rertzer/MoovUp/toPrint/forarm/robpart2V4.stl

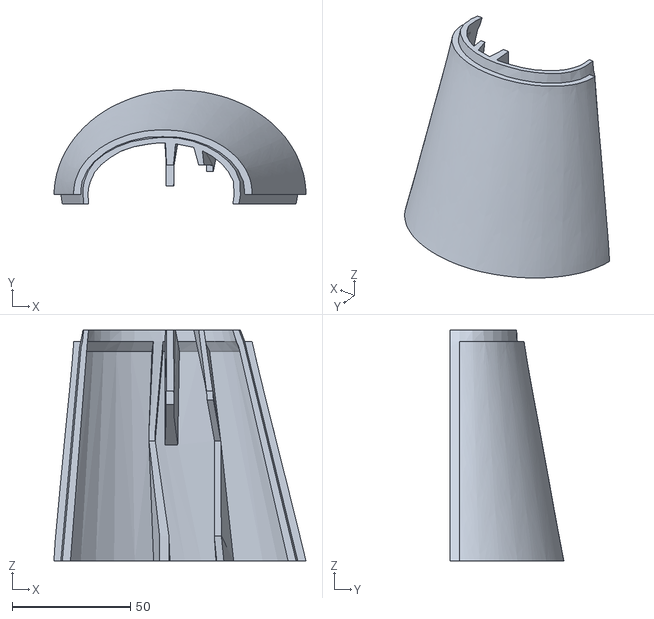
[picture p16: CAD file, 2025-05-26]
toPrint/forarm/robpart2V4.stl
106.4 x 48.1 x 97.5
