rertzer/MoovUp/toPrint/hand/i2_WristLargeV2.stl

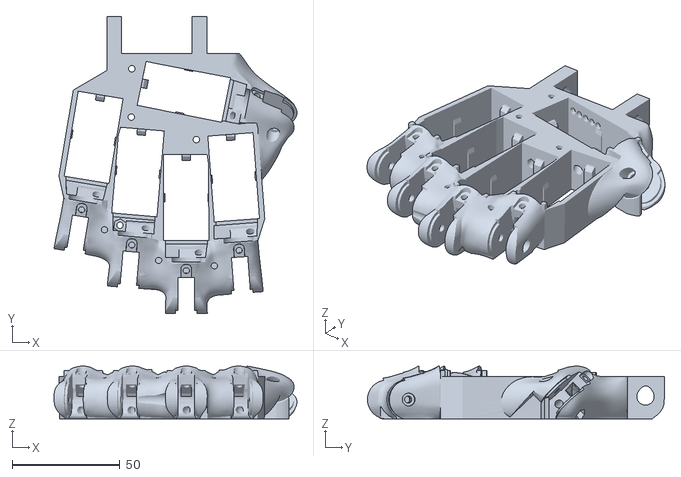
[picture p17: CAD file, 2025-05-26]
toPrint/hand/i2_WristLargeV2.stl
112.6 x 137.7 x 24.5
