rertzer/MoovUp/toPrint/motor/motorAdaptor.stl

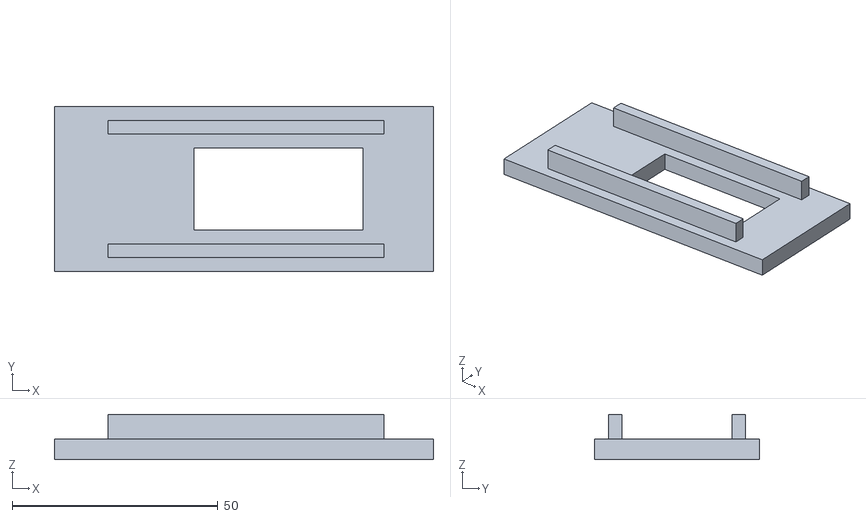
[picture p18: CAD file, 2025-06-15]
toPrint/motor/motorAdaptor.stl
92.0 x 40.0 x 11.0
