rertzer/MoovUp/toPrint/shoulder/PivMitV2.stl

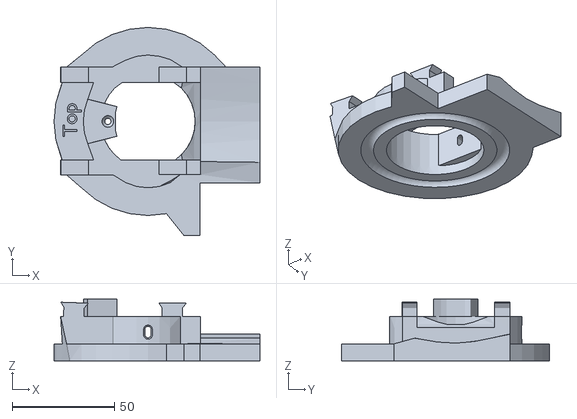
[picture p19: CAD file, 2025-06-15]
toPrint/shoulder/PivMitV2.stl
100.6 x 101.6 x 30.2
