rertzer/MoovUp/toPrint/wrist/RotaWrist3V3.stl

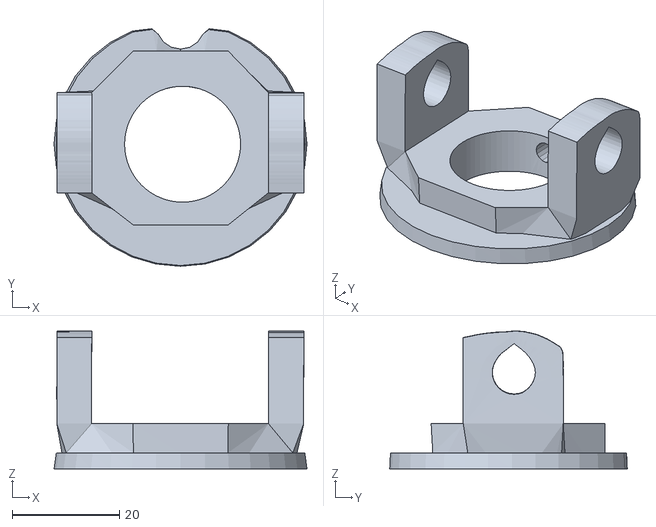
[picture p20: CAD file, 2025-05-26]
toPrint/wrist/RotaWrist3V3.stl
47.2 x 44.3 x 25.7
