rertzer/MoovUp/toPrint/bicep/RotWormV5.stl

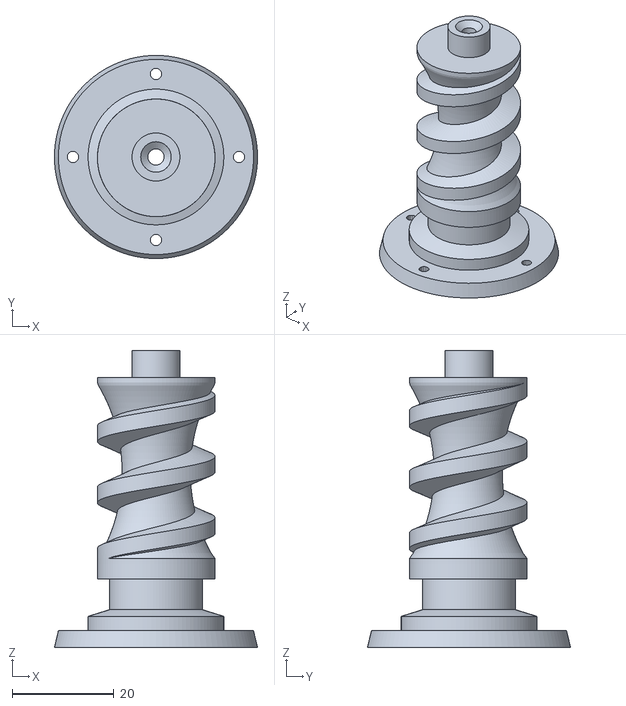
[picture p21: CAD file, 2025-05-26]
toPrint/bicep/RotWormV5.stl
40.0 x 39.9 x 58.4
