rertzer/MoovUp/toPrint/extra/entretoise.stl

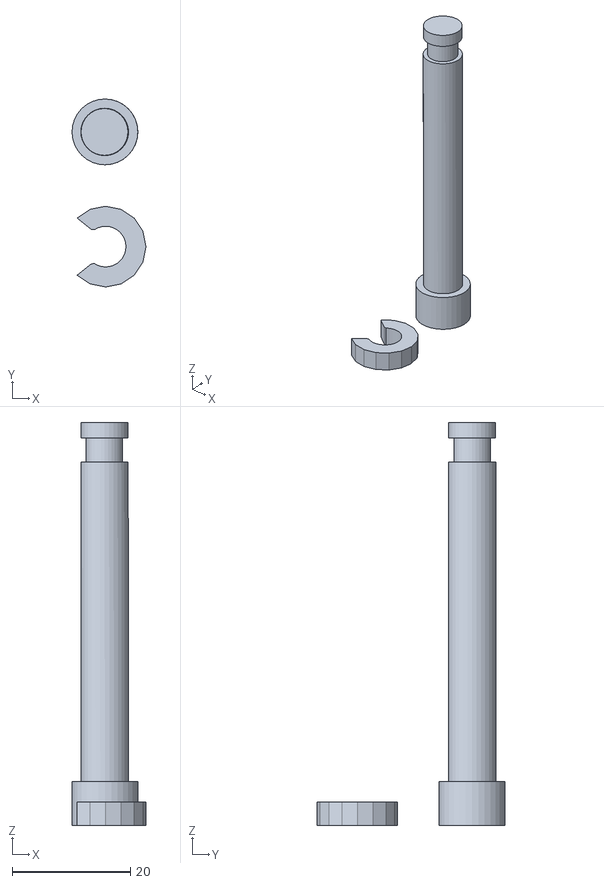
[picture p22: CAD file, 2025-06-15]
toPrint/extra/entretoise.stl
12.5 x 31.8 x 68.1
