rertzer/MoovUp/toPrint/forarm/RobRingV3.stl

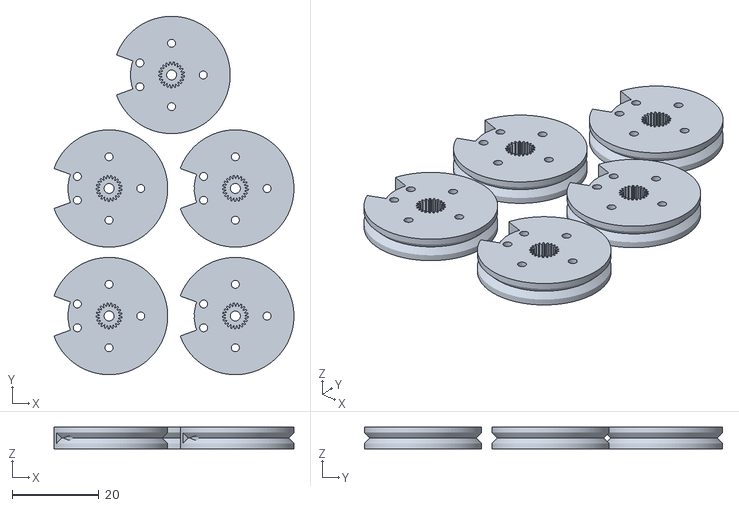
[picture p23: CAD file, 2025-05-26]
toPrint/forarm/RobRingV3.stl
55.3 x 82.5 x 5.00
