rertzer/MoovUp/toPrint/hand/color/i2_HandCoverV2.stl

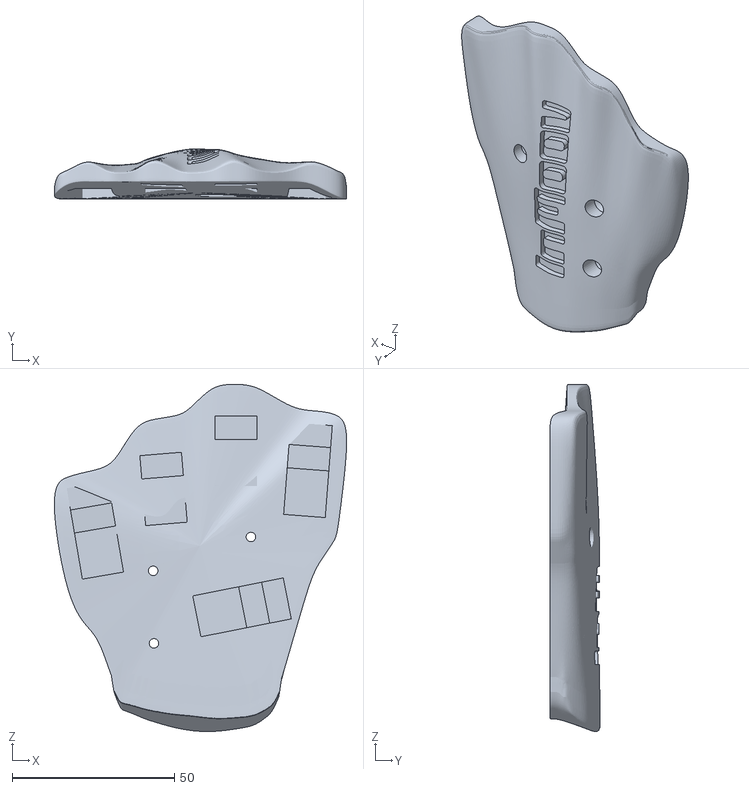
[picture p24: CAD file, 2025-05-26]
toPrint/hand/color/i2_HandCoverV2.stl
90.2 x 15.6 x 107.1
