rertzer/MoovUp/toPrint/hand/i2_FingersX5V2.stl

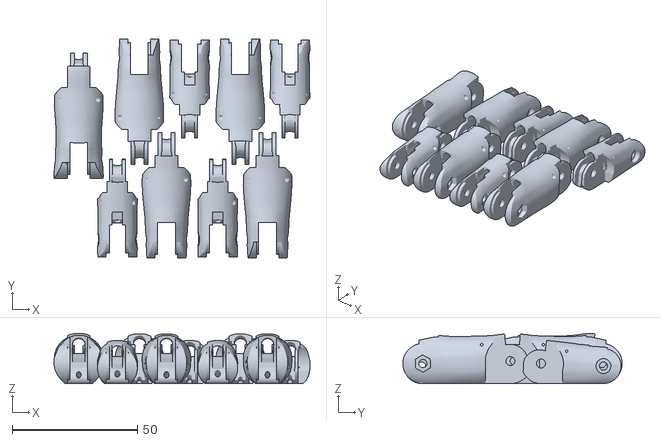
[picture p25: CAD file, 2025-05-26]
toPrint/hand/i2_FingersX5V2.stl
102.3 x 87.7 x 20.0
