rertzer/MoovUp/toPrint/motor/servoDiskShoulder.stl

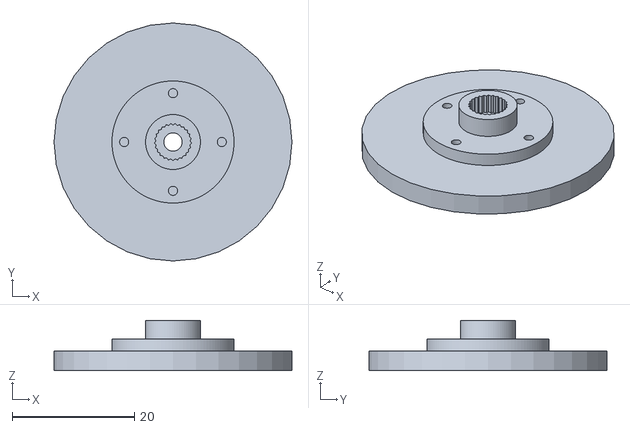
[picture p26: CAD file, 2025-06-15]
toPrint/motor/servoDiskShoulder.stl
39.0 x 39.0 x 8.20
