rertzer/MoovUp/toPrint/wrist/RotaWrist2V3.stl

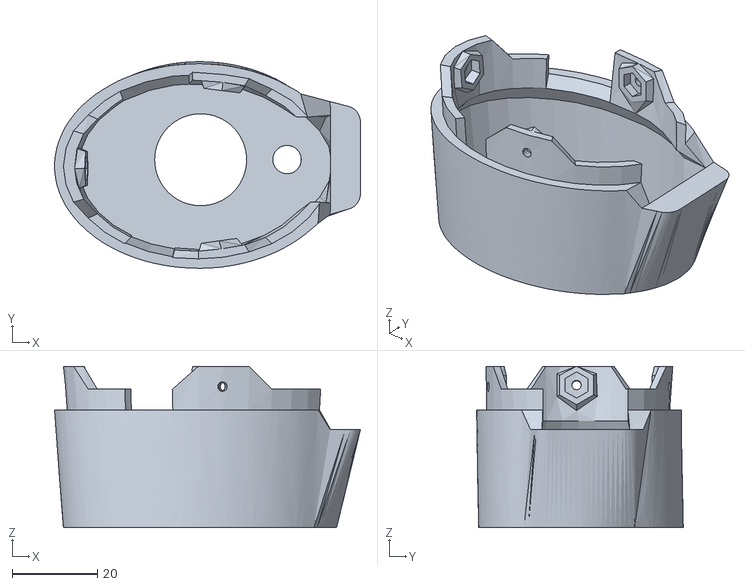
[picture p27: CAD file, 2025-05-26]
toPrint/wrist/RotaWrist2V3.stl
71.9 x 48.6 x 38.0
