rertzer/MoovUp/toPrint/bicep/HighArmSideV3.stl

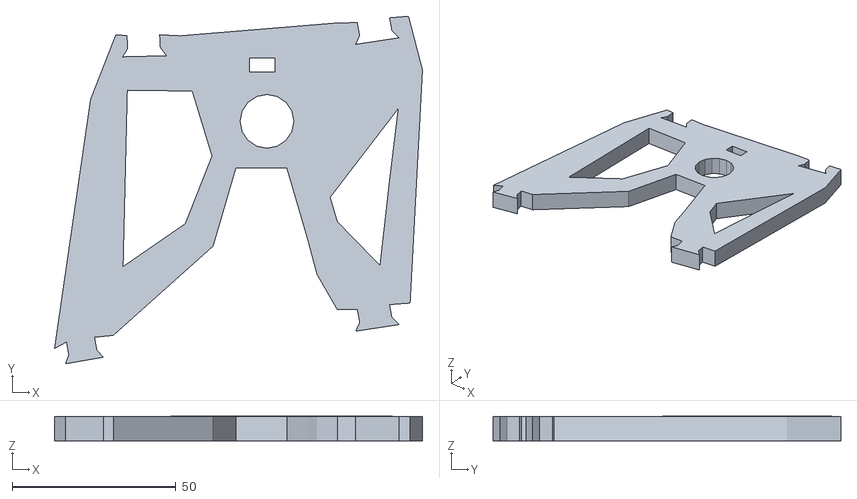
[picture p28: CAD file, 2025-05-26]
toPrint/bicep/HighArmSideV3.stl
112.4 x 106.1 x 7.50
