rertzer/MoovUp/toPrint/forarm/TensionerRightV1.stl

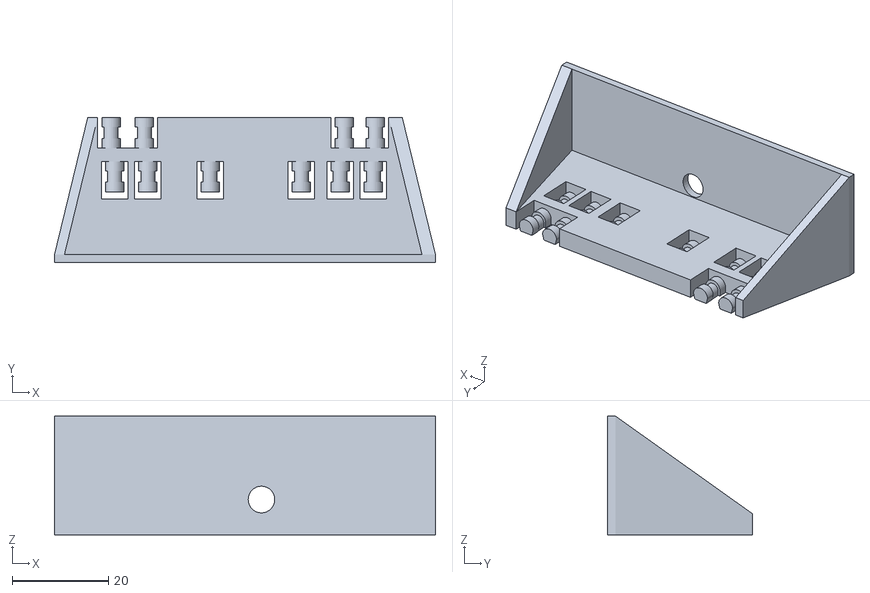
[picture p29: CAD file, 2025-05-26]
toPrint/forarm/TensionerRightV1.stl
79.3 x 30.3 x 24.7
