rertzer/MoovUp/toPrint/hand/color/i2_CoverFingerV3.stl

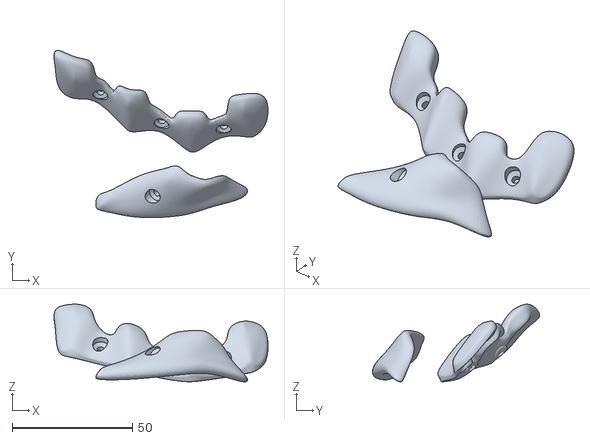
[picture p30: CAD file, 2025-05-26]
toPrint/hand/color/i2_CoverFingerV3.stl
89.0 x 69.6 x 32.3
