rertzer/MoovUp/toPrint/hand/i2_WristGearV1.stl

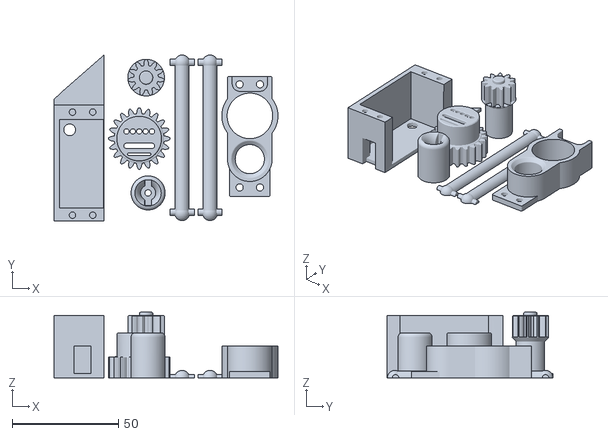
[picture p31: CAD file, 2025-05-26]
toPrint/hand/i2_WristGearV1.stl
105.2 x 78.1 x 30.8
