rertzer/MoovUp/toPrint/motor/motorAdaptorBis.stl

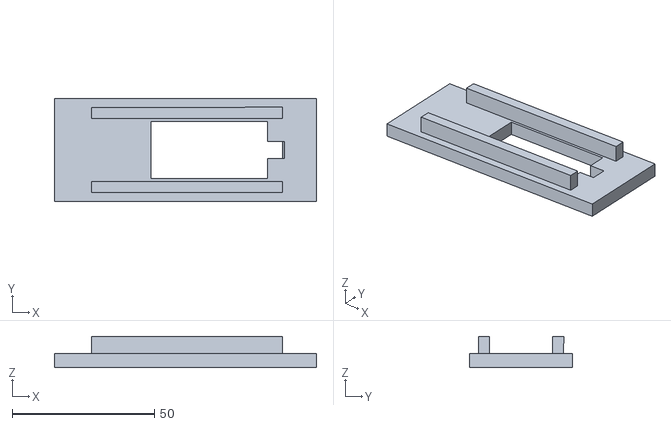
[picture p32: CAD file, 2025-06-15]
toPrint/motor/motorAdaptorBis.stl
92.0 x 36.0 x 11.0
