rertzer/MoovUp/toPrint/wrist/RotaWrist1V4.stl

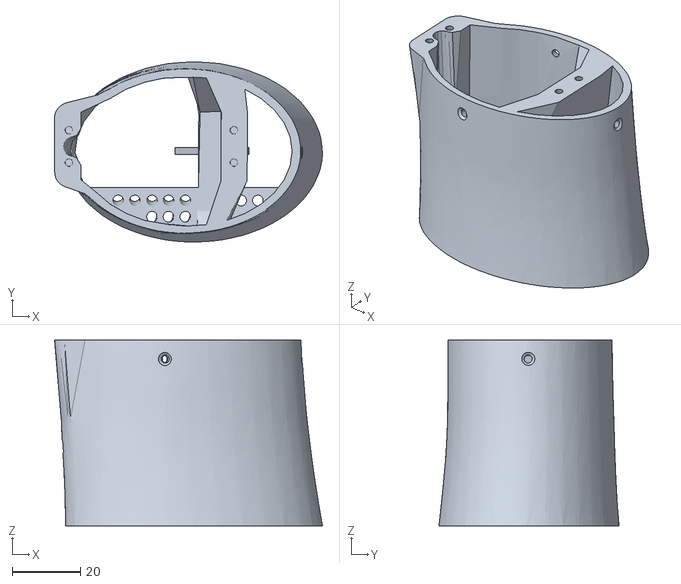
[picture p33: CAD file, 2025-05-26]
toPrint/wrist/RotaWrist1V4.stl
78.6 x 52.8 x 54.5
