rertzer/MoovUp/toPrint/bicep/PistonanticlockV2.stl

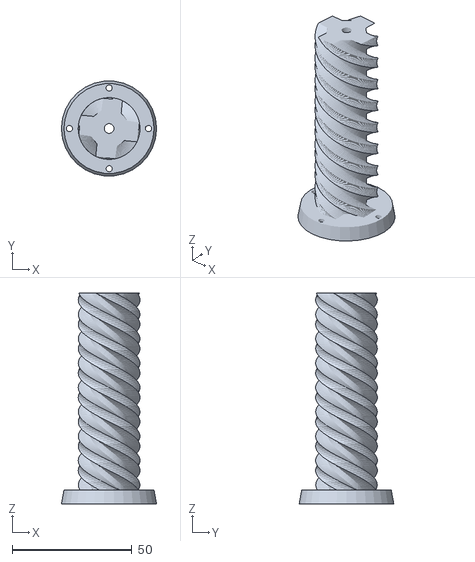
[picture p34: CAD file, 2025-05-26]
toPrint/bicep/PistonanticlockV2.stl
39.7 x 39.5 x 88.0
