rertzer/MoovUp/toPrint/forarm/RobCableBackV3.stl

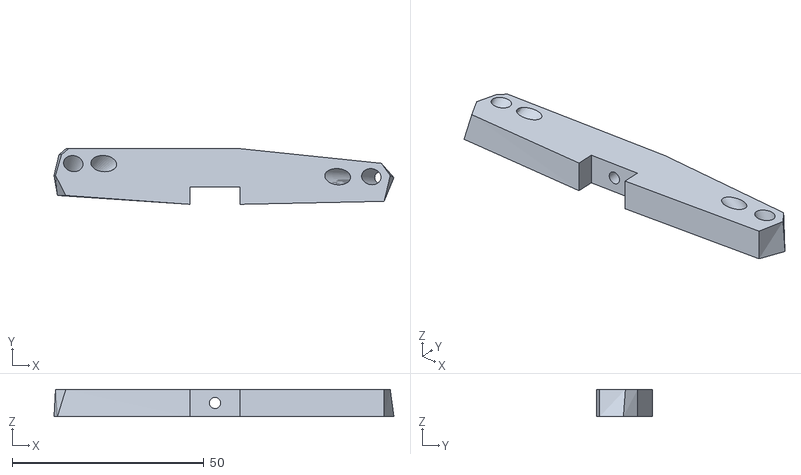
[picture p35: CAD file, 2025-05-26]
toPrint/forarm/RobCableBackV3.stl
88.7 x 14.5 x 7.17
