rertzer/MoovUp/toPrint/hand/i2_PulleyX5V1.stl

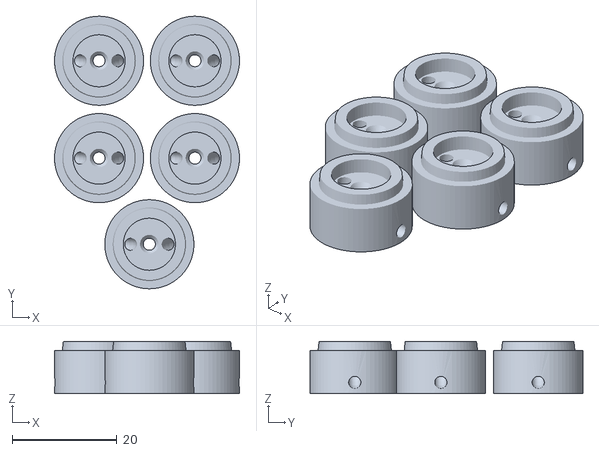
[picture p36: CAD file, 2025-05-26]
toPrint/hand/i2_PulleyX5V1.stl
35.3 x 52.0 x 10.0
