rertzer/MoovUp/toPrint/wrist/CableHolderWristV5.stl

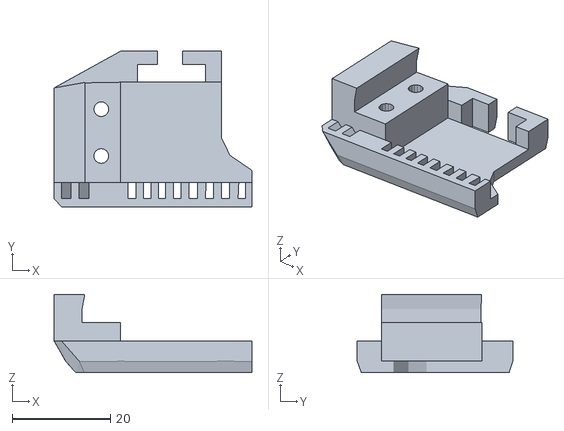
[picture p37: CAD file, 2025-05-26]
toPrint/wrist/CableHolderWristV5.stl
40.2 x 31.6 x 15.8
