rertzer/MoovUp/toPrint/bicep/PivPotentioRoundV3.stl

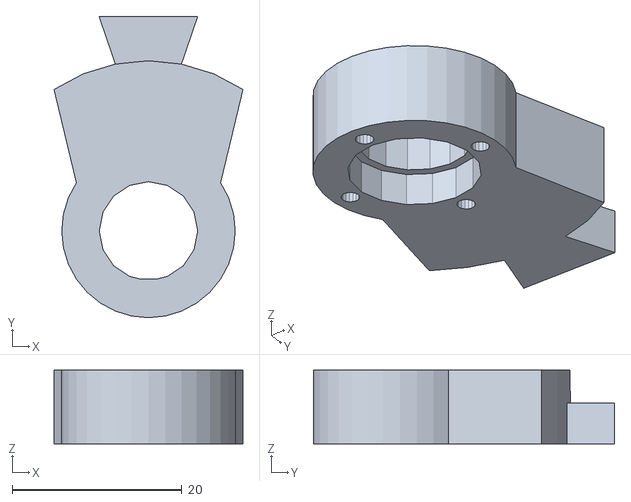
[picture p38: CAD file, 2025-05-26]
toPrint/bicep/PivPotentioRoundV3.stl
22.3 x 35.5 x 8.68
