rertzer/MoovUp/toPrint/forarm/robpart5V4.stl

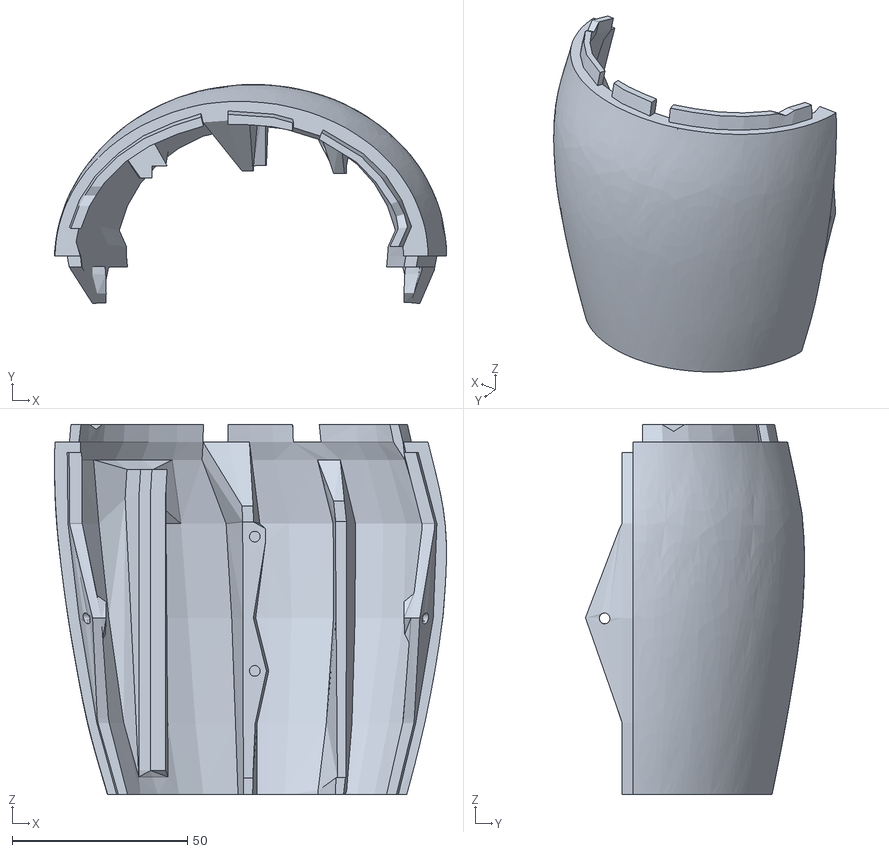
[picture p39: CAD file, 2025-05-26]
toPrint/forarm/robpart5V4.stl
111.8 x 62.5 x 105.6
