rertzer/MoovUp/toPrint/bicep/servobaseV1.stl

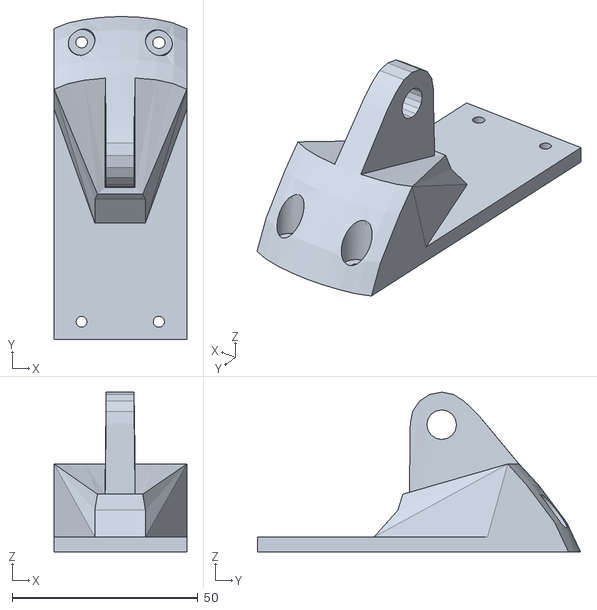
[picture p40: CAD file, 2025-05-26]
toPrint/bicep/servobaseV1.stl
35.7 x 87.0 x 43.1
