rertzer/MoovUp/toPrint/forarm/servo-pulleyX5.stl

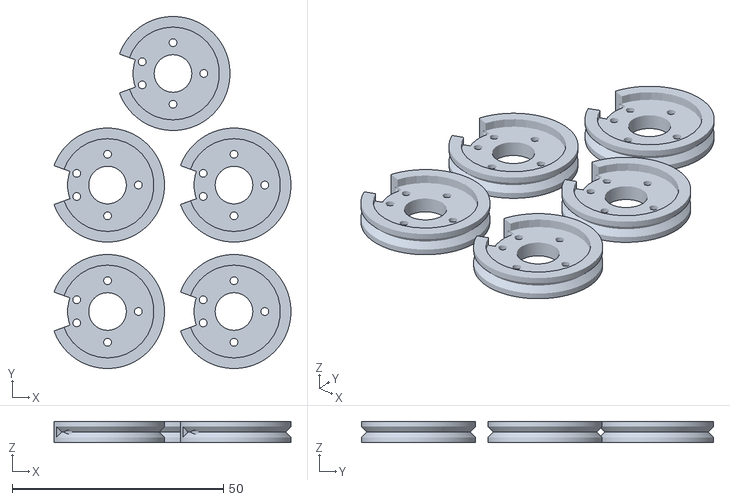
[picture p41: CAD file, 2025-05-26]
toPrint/forarm/servo-pulleyX5.stl
56.1 x 83.4 x 5.00
