rertzer/MoovUp/toPrint/bicep/elbowshaftgearV1.stl

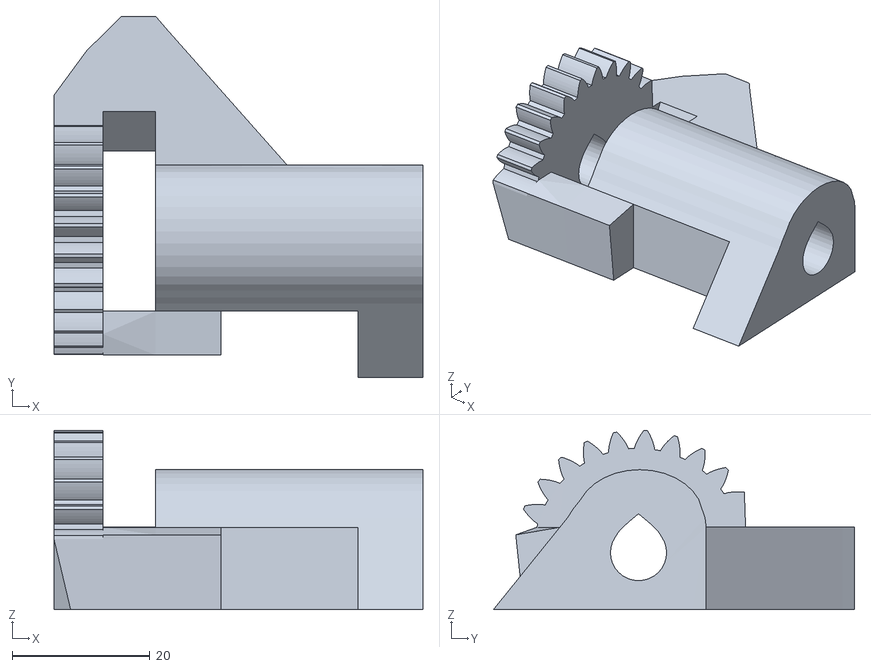
[picture p42: CAD file, 2025-05-26]
toPrint/bicep/elbowshaftgearV1.stl
53.5 x 52.4 x 26.0
