rertzer/MoovUp/toPrint/forarm/RobCableFrontV3.stl

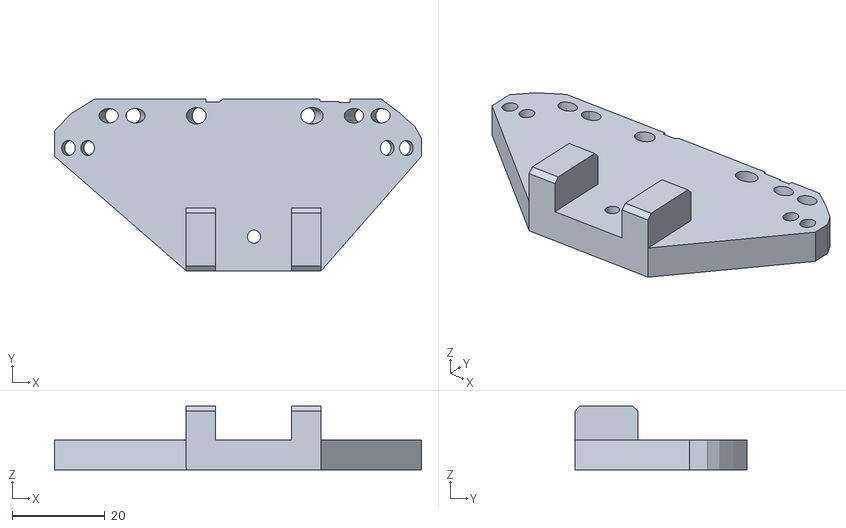
[picture p43: CAD file, 2025-05-26]
toPrint/forarm/RobCableFrontV3.stl
79.3 x 37.1 x 13.8
