rertzer/MoovUp/toPrint/bicep/armtopcover1.stl

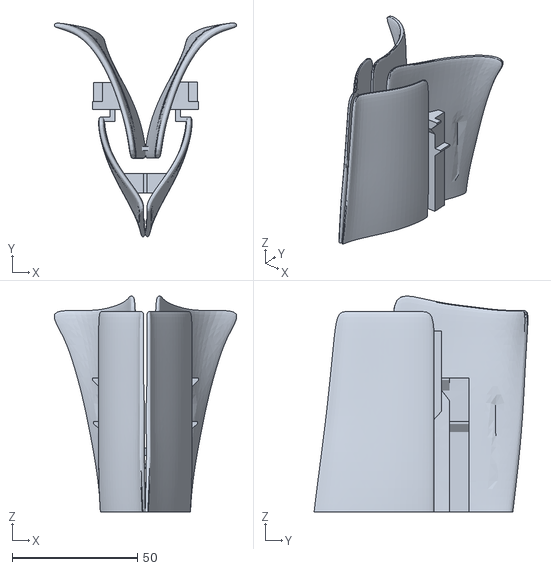
[picture p44: CAD file, 2025-05-26]
toPrint/bicep/armtopcover1.stl
72.7 x 85.2 x 86.1
