rertzer/MoovUp/toPrint/forarm/robcap3V2.stl

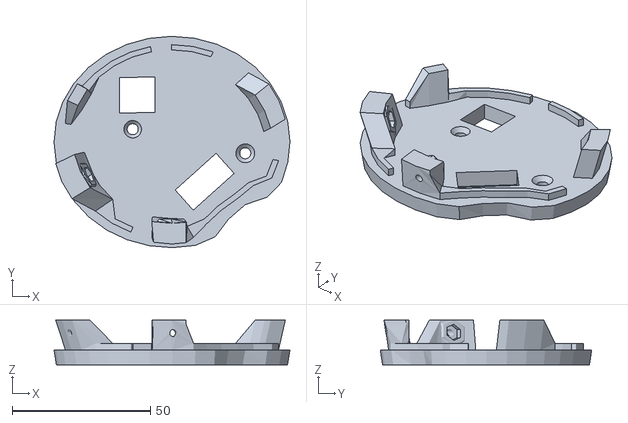
[picture p45: CAD file, 2025-05-26]
toPrint/forarm/robcap3V2.stl
85.5 x 76.5 x 16.2
