rertzer/MoovUp/toPrint/bicep/RotcenterV3.stl

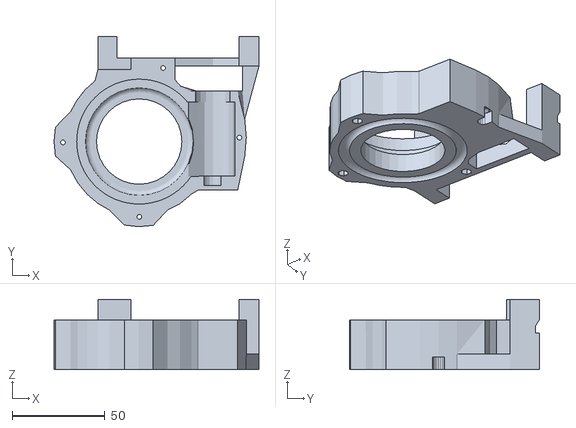
[picture p46: CAD file, 2025-05-26]
toPrint/bicep/RotcenterV3.stl
110.5 x 102.6 x 37.8
