rertzer/MoovUp/toPrint/forarm/RobServoBedV6.stl

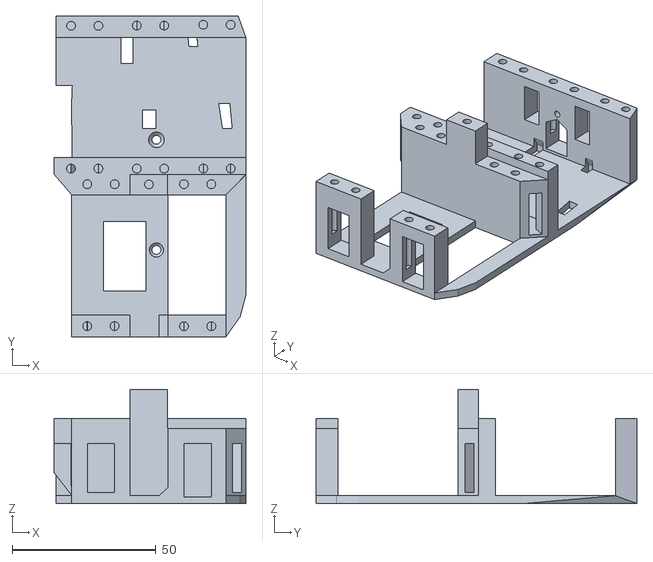
[picture p47: CAD file, 2025-05-26]
toPrint/forarm/RobServoBedV6.stl
66.7 x 111.6 x 39.7
