rertzer/MoovUp/toPrint/bicep/RotMitV3.stl

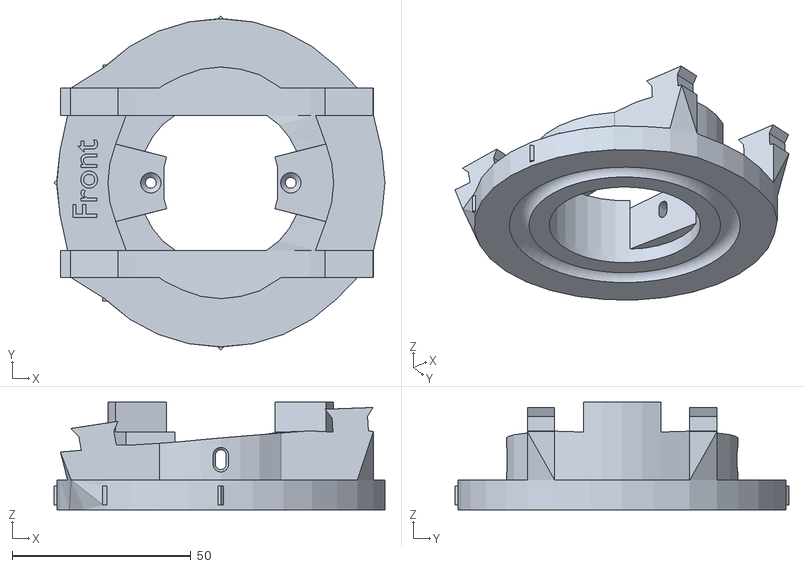
[picture p48: CAD file, 2025-05-26]
toPrint/bicep/RotMitV3.stl
92.6 x 93.4 x 30.2
