rertzer/MoovUp/toPrint/forarm/robpart3V4.stl

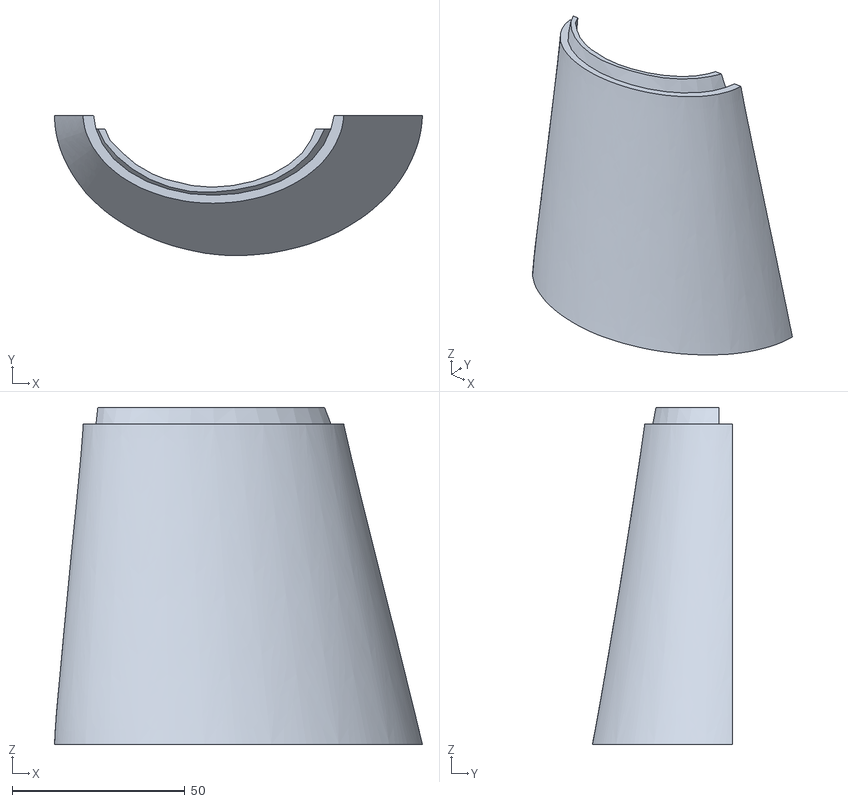
[picture p49: CAD file, 2025-05-26]
toPrint/forarm/robpart3V4.stl
106.4 x 40.6 x 97.5
