rertzer/MoovUp/toPrint/bicep/servoholderV1.stl

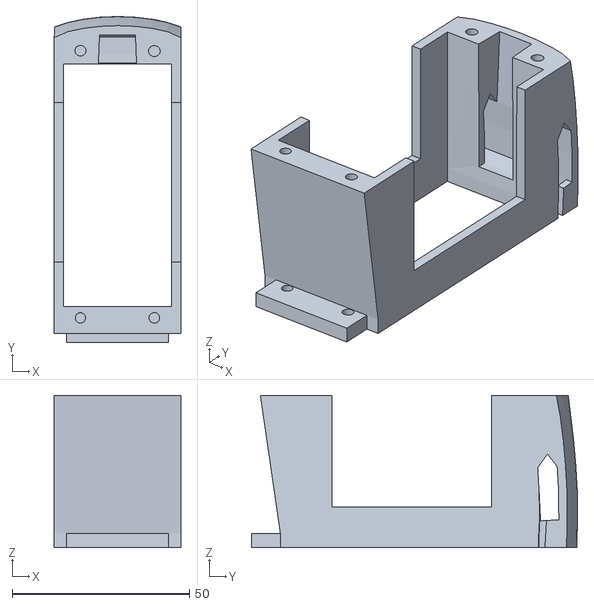
[picture p50: CAD file, 2025-05-26]
toPrint/bicep/servoholderV1.stl
35.8 x 91.9 x 42.9
