rertzer/MoovUp/toPrint/bicep/spacerV1.stl

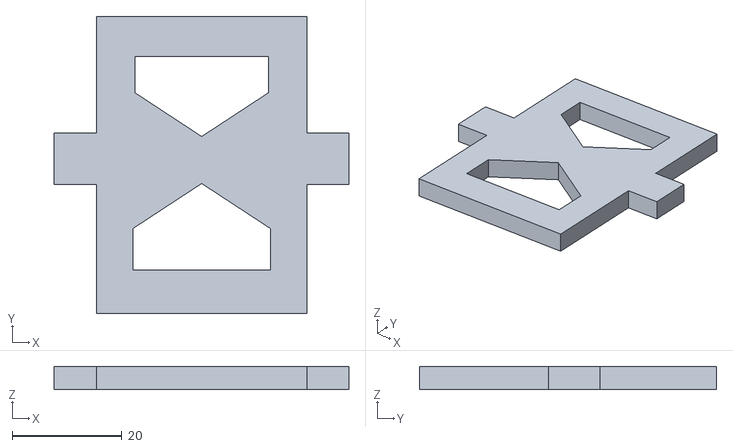
[picture p51: CAD file, 2025-05-26]
toPrint/bicep/spacerV1.stl
53.8 x 54.3 x 4.23
