rertzer/MoovUp/toPrint/bicep/ReinforcerV2.stl

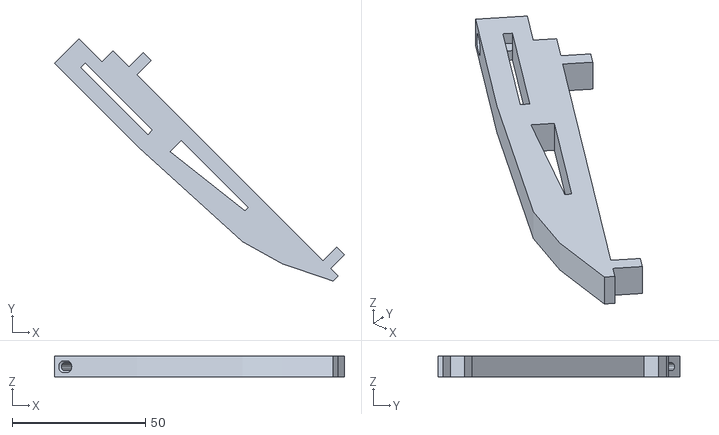
[picture p52: CAD file, 2025-05-26]
toPrint/bicep/ReinforcerV2.stl
108.8 x 90.9 x 7.77
