rertzer/MoovUp/toPrint/bicep/RotGearV6.stl

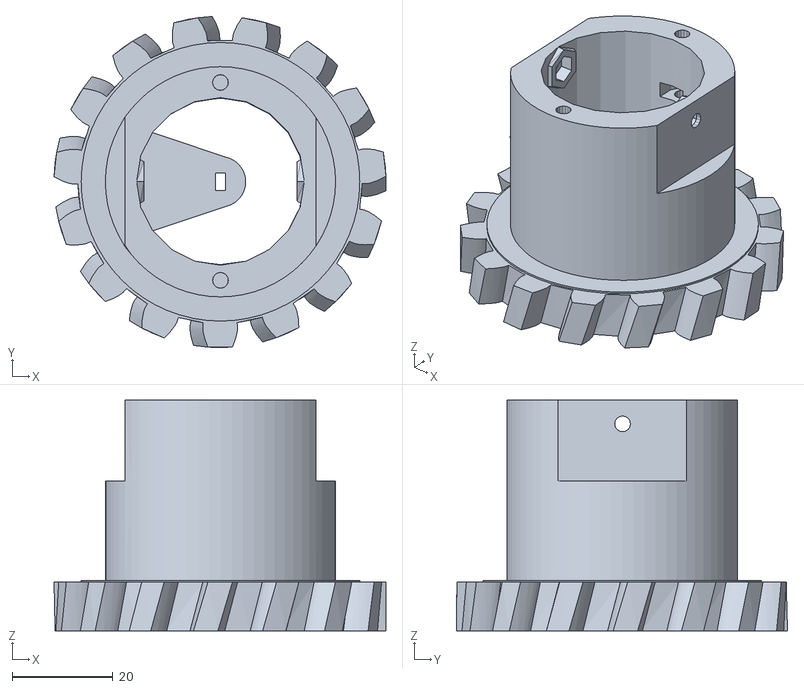
[picture p53: CAD file, 2025-05-26]
toPrint/bicep/RotGearV6.stl
65.7 x 65.6 x 45.7
