rertzer/MoovUp/toPrint/bicep/RibonPusherV1.stl

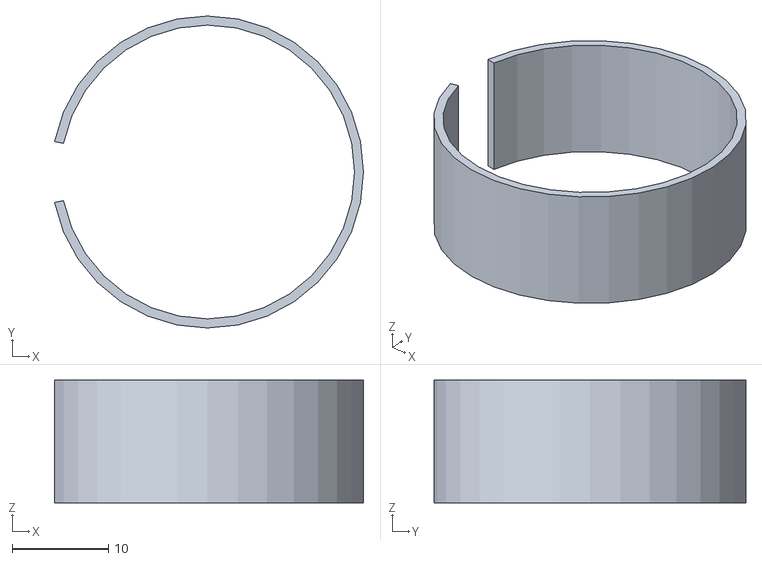
[picture p54: CAD file, 2025-05-26]
toPrint/bicep/RibonPusherV1.stl
32.0 x 32.3 x 12.7
