rertzer/MoovUp/toPrint/bicep/PistonbaseantiV2.stl

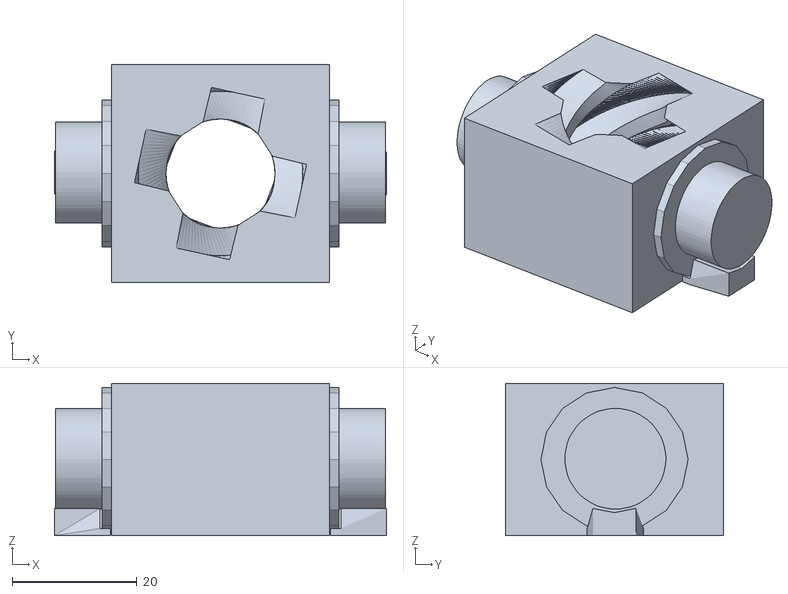
[picture p55: CAD file, 2025-05-26]
toPrint/bicep/PistonbaseantiV2.stl
53.3 x 35.0 x 24.5
