rertzer/MoovUp/toPrint/bicep/RotTitV4.stl

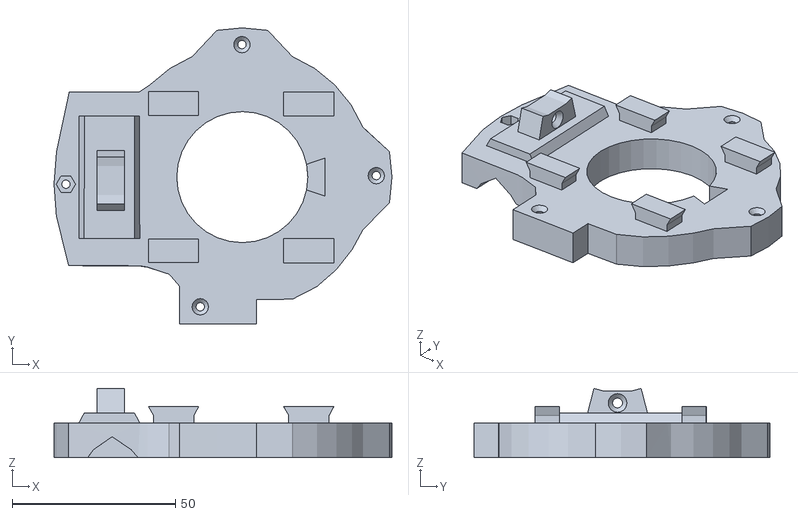
[picture p56: CAD file, 2025-05-26]
toPrint/bicep/RotTitV4.stl
103.5 x 90.7 x 21.2
