rertzer/MoovUp/toPrint/bicep/LowArmSideV3.stl

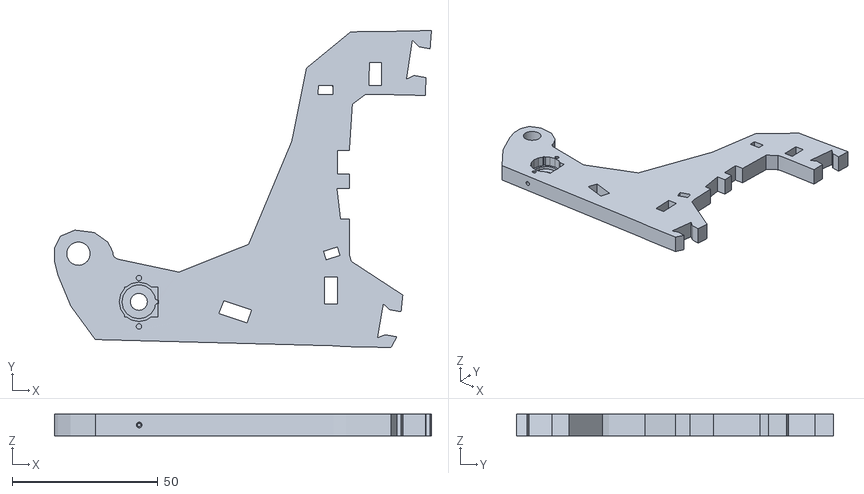
[picture p57: CAD file, 2025-05-26]
toPrint/bicep/LowArmSideV3.stl
129.1 x 108.6 x 7.50
