rertzer/MoovUp/code/include/MotorThumb.hpp

#ifndef MOTOR_THUMB_HPP
#define MOTOR_THUMB_HPP

#include "Motor.hpp"

class MotorThumb : public Motor {
   public:
	MotorThumb(uint16_t start_pos);
	MotorThumb(MotorThumb const& m);
	~MotorThumb();
	MotorThumb& operator=(MotorThumb const& m);

	uint16_t getPosition() const;
	void	 setPosition(uint16_t pos);

   private:
};

#endif
