rertzer/MoovUp/code/src/arm/Ring.cpp

#include "Ring.hpp"

Ring::Ring() : Finger(sensor_pin, motor_default), motor(motor_default.start) {}

Ring::Ring(Ring const& r) : Finger(r.sensor.getPin(), r.motor_setup), motor(r.motor) {
	*this = r;
}

Ring::~Ring() {}

Ring& Ring::operator=(Ring const& r) {
	if (this != &r) {
		Finger::operator=(r);
		motor = r.motor;
	}
	return (*this);
}

void Ring::move() {
	updatePos();
	motor.setPosition(pos);
}

void Ring::reset() {
	motor_setup = motor_default;
	target = motor_default.start;
	mode = MoveMode::POSITION;
}

constexpr uint8_t			   Ring::sensor_pin;
constexpr Joint::motor_setup_t Ring::motor_default;
